jannisbecker/ball_balancing_robot/cad/Motor.SLDPRT

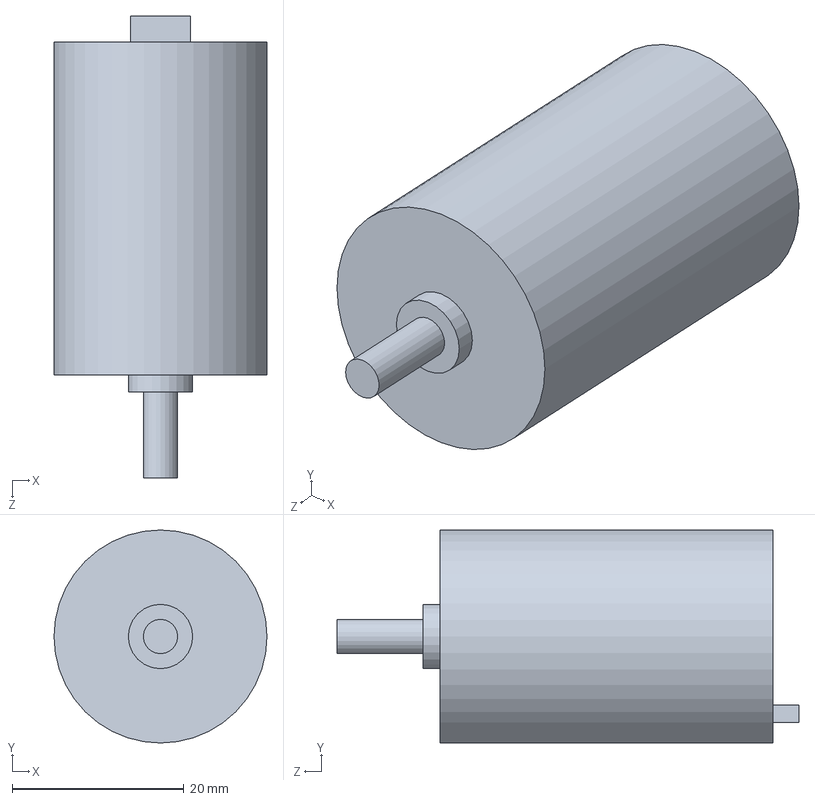
[picture p29: CAD file, 2017-08-12]
cad/Motor.SLDPRT
24.8 x 24.8 x 53.8 mm
