jannisbecker/ball_balancing_robot/cad/Motor Mount Plate.SLDPRT

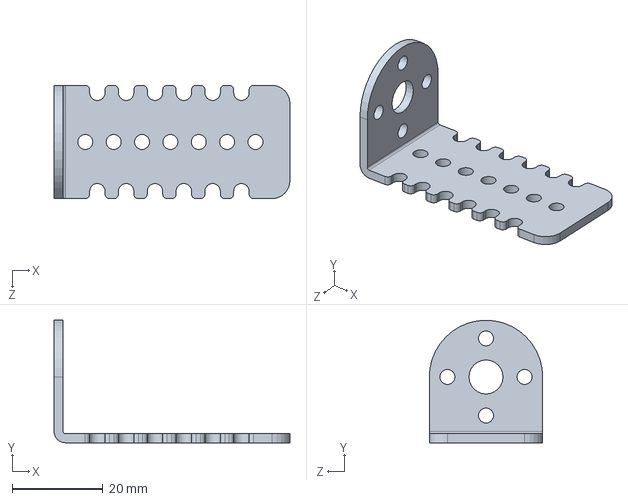
[picture p30: CAD file, 2017-08-12]
cad/Motor Mount Plate.SLDPRT
52.0 x 27.0 x 25.0 mm
