jannisbecker/ball_balancing_robot/cad/Motor Mount.SLDPRT

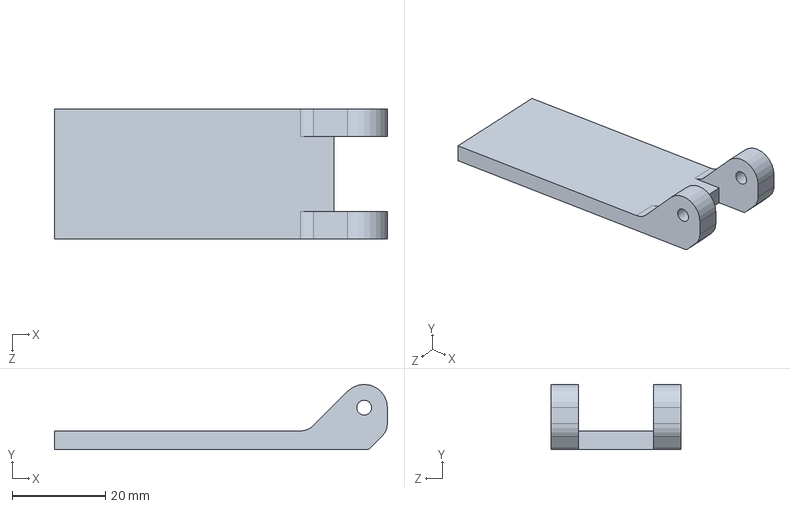
[picture p31: CAD file, 2017-08-12]
cad/Motor Mount.SLDPRT
71.5 x 14.0 x 28.0 mm
