jannisbecker/ball_balancing_robot/cad/ArduinoMega2560.SLDPRT

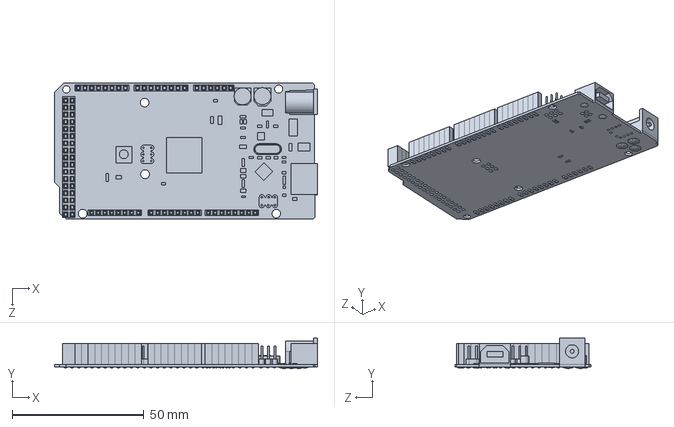
[picture p32: CAD file, 2017-08-12]
cad/ArduinoMega2560.SLDPRT
100.0 x 11.6 x 51.6 mm
