jannisbecker/ball_balancing_robot/cad/IMU_Tower Rework 2.SLDPRT

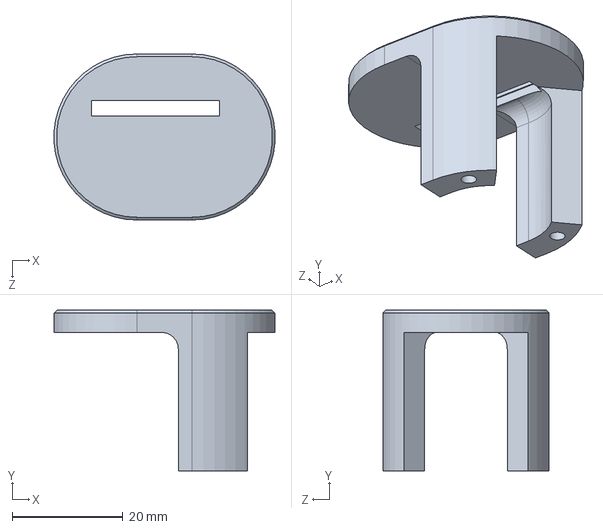
[picture p33: CAD file, 2017-08-12]
cad/IMU_Tower Rework 2.SLDPRT
39.9 x 29.0 x 30.0 mm
